shrimp-18/Whimsy-Cam/images/camback.png

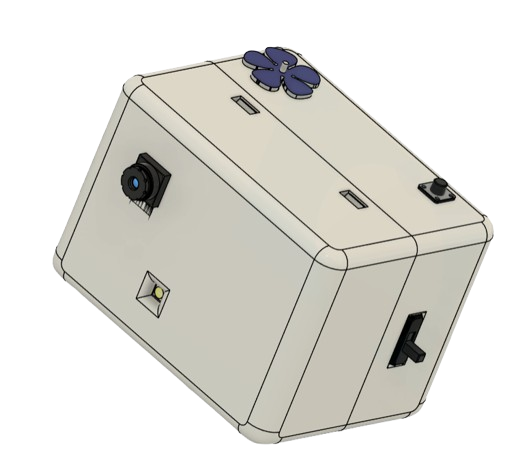
images/camback.png
