shrimp-18/Whimsy-Cam/images/idea.png

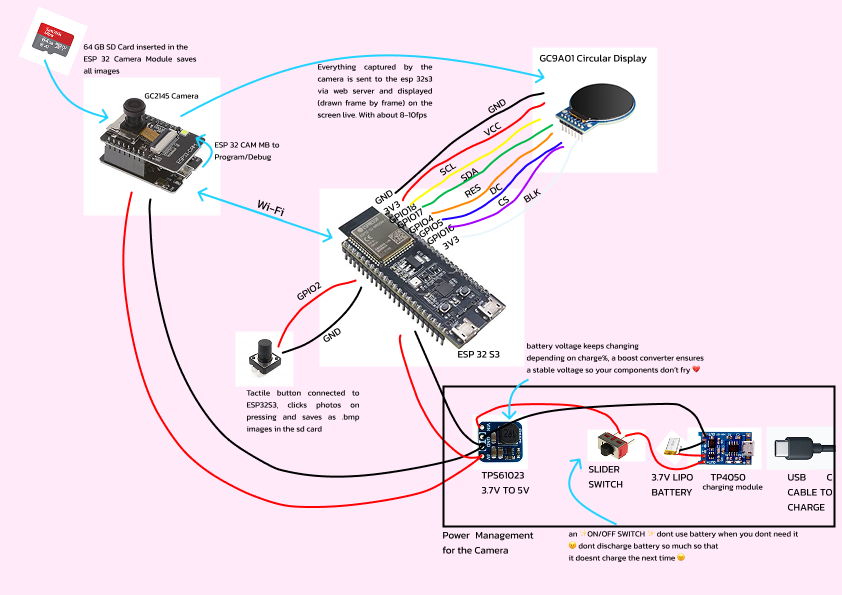
images/idea.png
