shrimp-18/Whimsy-Cam/images/zine.jpg

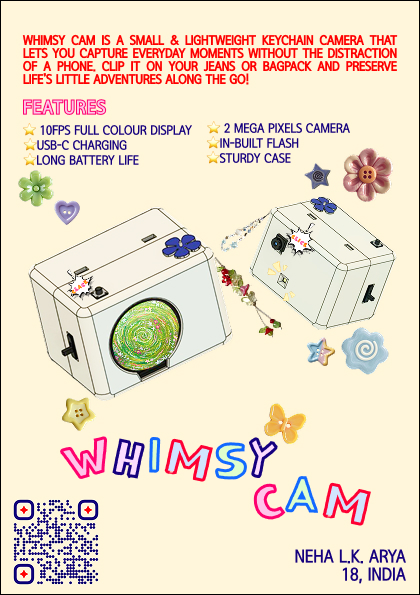
images/zine.jpg
