shrimp-18/Whimsy-Cam/src/cad/assets/ESP32-S3-WROOM-1-3.JPG

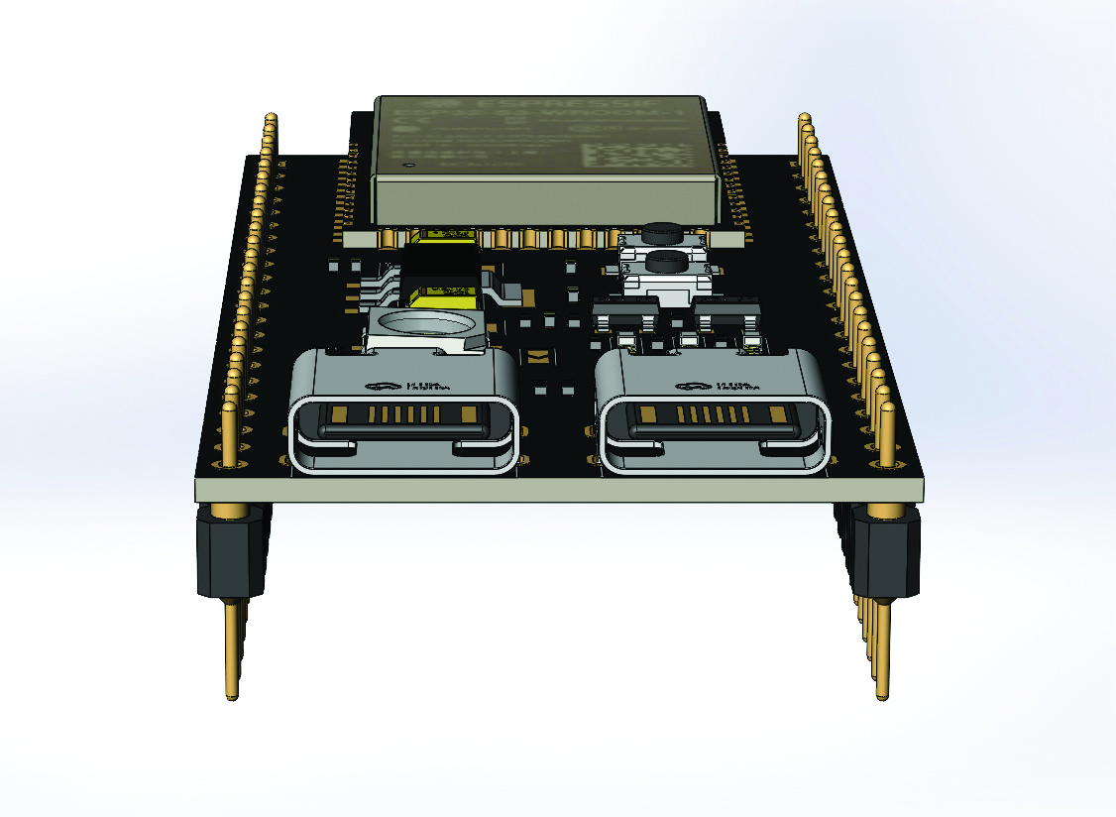
src/cad/assets/ESP32-S3-WROOM-1-3.JPG
