shrimp-18/Whimsy-Cam/src/cad/assets/LCD 1.28 Inch GC9A01.png

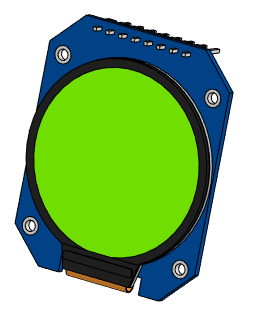
src/cad/assets/LCD 1.28 Inch GC9A01.png
