shrimp-18/Whimsy-Cam/src/cad/assets/Reset button 2.png

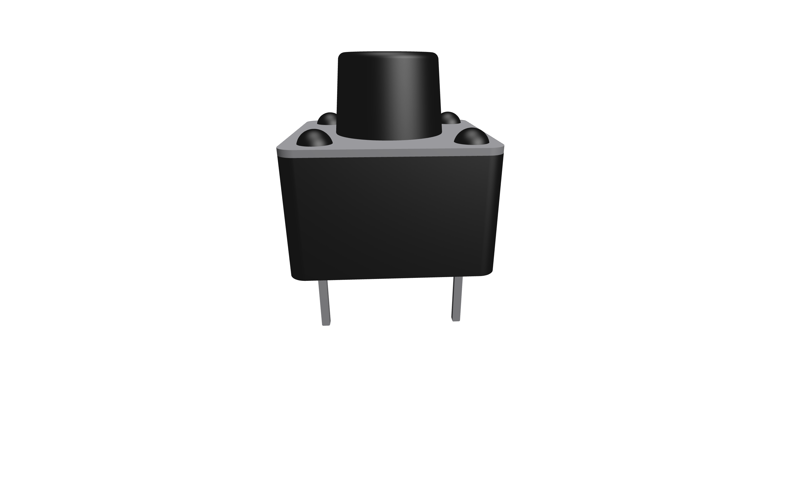
src/cad/assets/Reset button 2.png
