shrimp-18/Whimsy-Cam/src/cad/assets/ROSE PETAL TEMPLATE.png

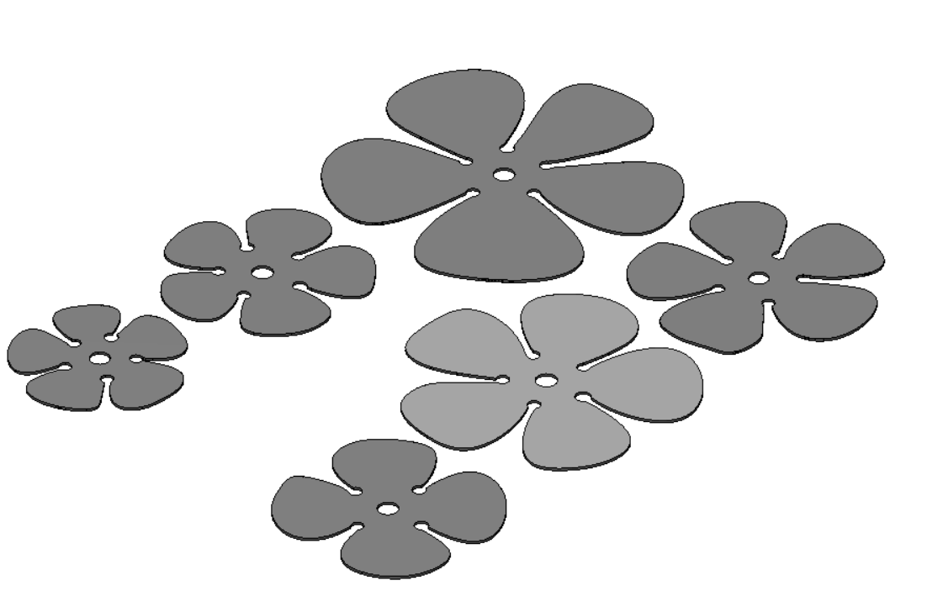
src/cad/assets/ROSE PETAL TEMPLATE.png
