shrimp-18/Whimsy-Cam/src/cad/assets/SLW-116641-3A-RA-S-D.png

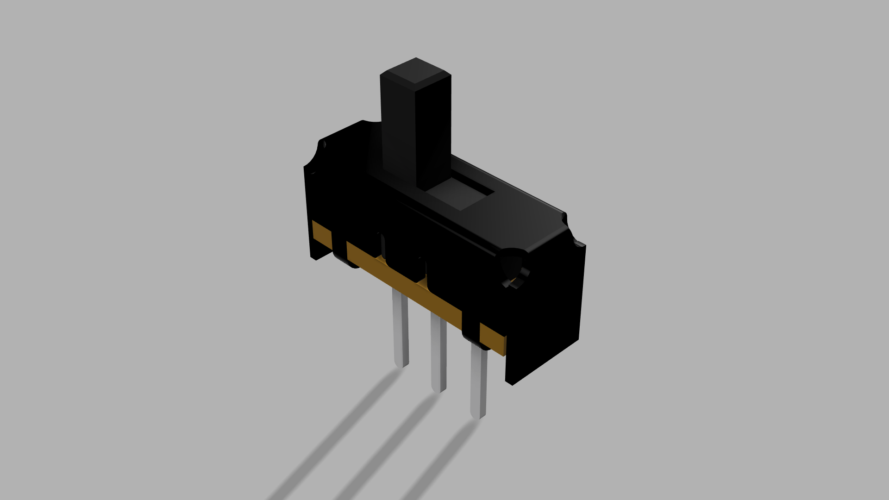
src/cad/assets/SLW-116641-3A-RA-S-D.png
